diepbaoquy97/SmartHome/Images/Enclosure2.jpg

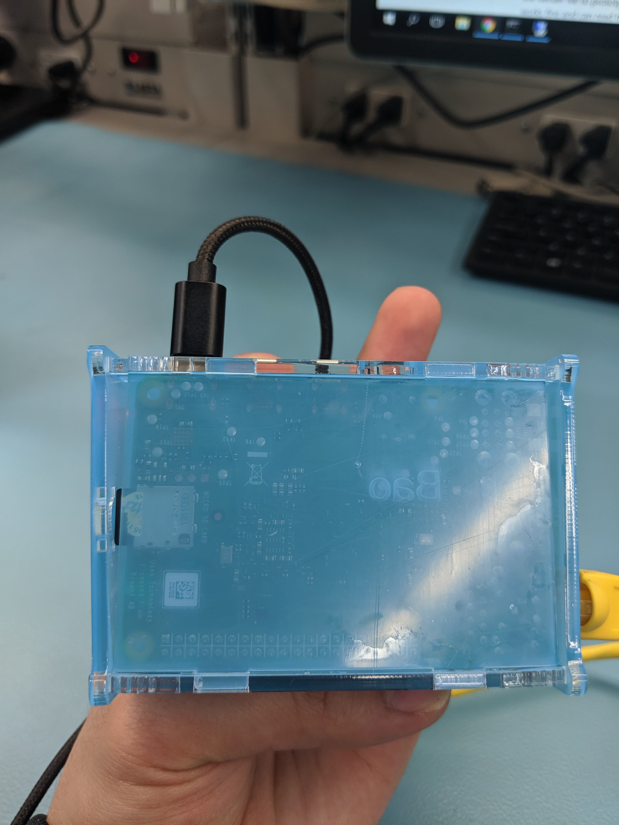
Images/Enclosure2.jpg
